rcland12/wardriving/case/images/back.jpeg

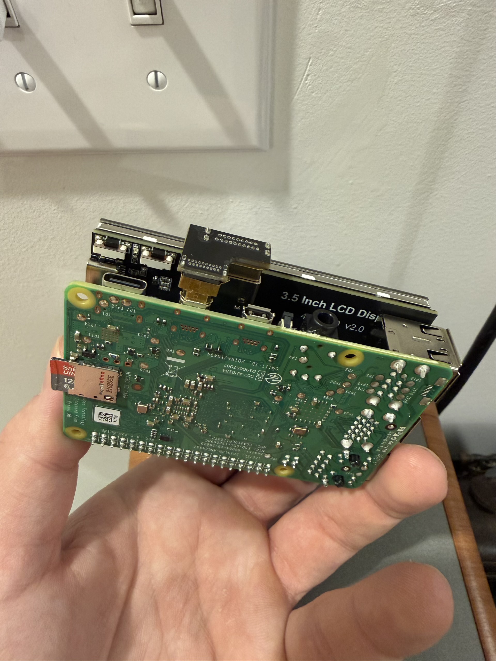
case/images/back.jpeg
