rcland12/wardriving/case/images/right.jpeg

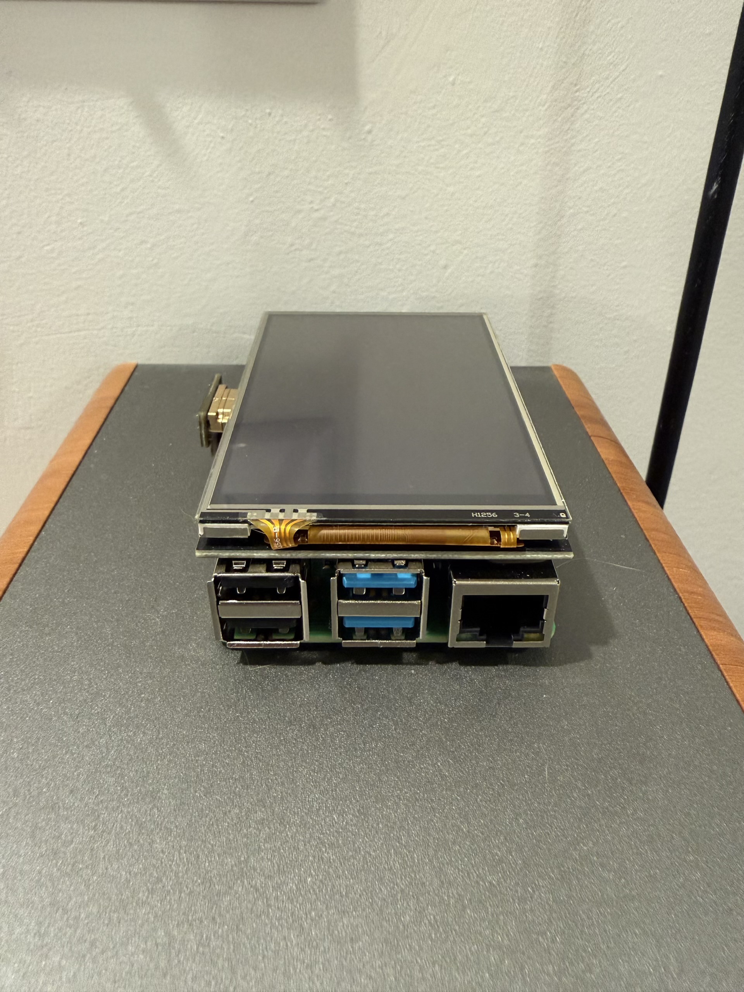
case/images/right.jpeg
